boorsteid4/snc-closedloop/Documentation/fig/LightControllerUML.png

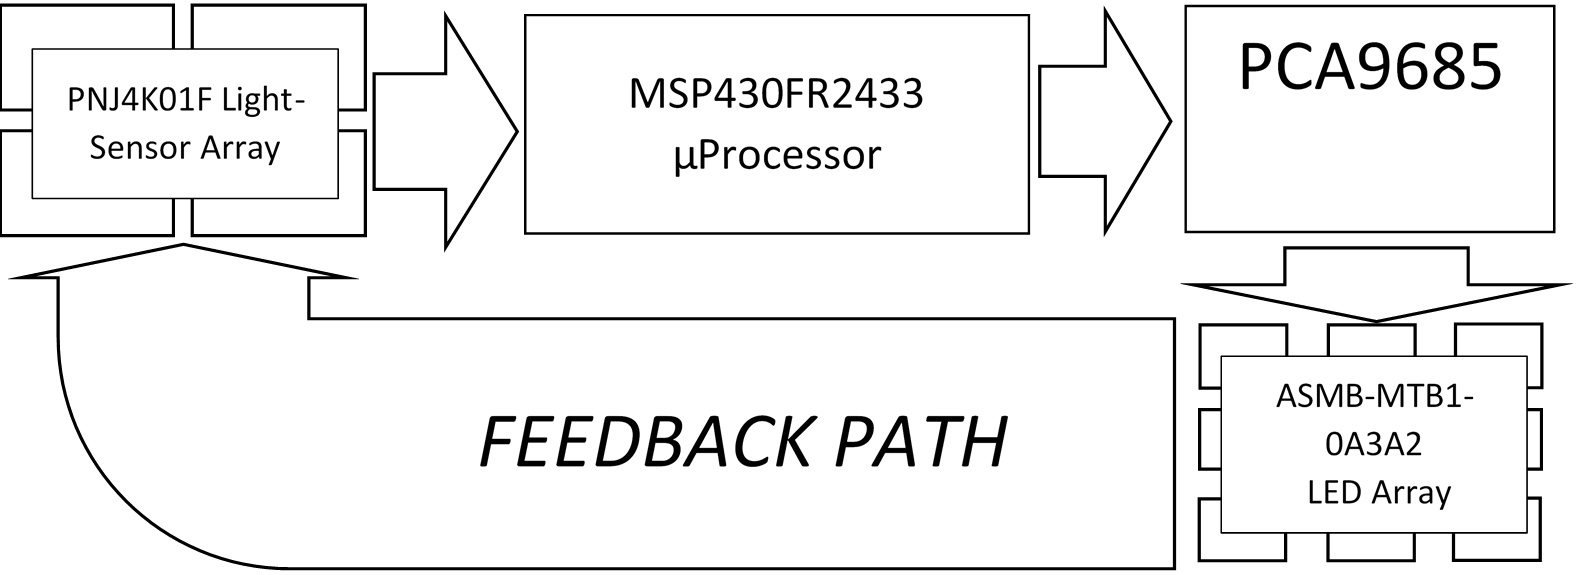
Documentation/fig/LightControllerUML.png
